dsonmaidinh/Differential-Wheel-Mobile-Robot/firmware/stm/app/app.h

/**
 * @file       app.h
 * @copyright  [Your Copyright]
 * @license    [Your License]
 * @version    1.0.0
 * @date       2026-03-02
 * @author     Dong Son
 *
 * @brief
 */
/* Define to prevent recursive inclusion ------------------------------ */
#ifndef INC_APP_H_
#define INC_APP_H_

/* Includes ----------------------------------------------------------- */
/* Public defines ----------------------------------------------------- */
/* Public enumerate/structure ----------------------------------------- */
/* Public macros ------------------------------------------------------ */
/* Public variables --------------------------------------------------- */
/* Public function prototypes ----------------------------------------- */
uint8_t app_init(void);

uint8_t app_process(void);

#endif /* INC_APP_H_ */

/* End of file -------------------------------------------------------- */
