dsonmaidinh/Differential-Wheel-Mobile-Robot/firmware/stm/sys/sys_task.h

/**
 * @file       sys_task.h
 * @copyright  [Your Copyright]
 * @license    [Your License]
 * @version    0.1.0
 * @date       2026-03-02
 * @author     Dong Son
 *
 * @brief      System Services Task Scheduler using TIM3 interrupt.
 */
/* Define to prevent recursive inclusion ------------------------------ */
#ifndef __SYS_TASK_H
#define __SYS_TASK_H
/* Includes ----------------------------------------------------------- */
#include <stdbool.h>
#include <stdint.h>

/* Public defines ----------------------------------------------------- */
/* Public enumerate/structure ----------------------------------------- */
typedef enum
{
  SRV_TASK_OK = 0,
  SRV_TASK_ERR,
  SRV_TASK_ERR_PARAM
} sys_task_err_t;
typedef void (*sys_task_cb_t)(void *arg);

/* Public macros ------------------------------------------------------ */
/* Public variables --------------------------------------------------- */
/* Public function prototypes ----------------------------------------- */
sys_task_err_t sys_task_init(void);
sys_task_err_t sys_task_process(void);

int            sys_task_add(sys_task_cb_t cb, void *arg, uint32_t period_ms, uint32_t delay_ms);
sys_task_err_t sys_task_del(int id);
sys_task_err_t sys_task_start(int id);
sys_task_err_t sys_task_stop(int id);
sys_task_err_t sys_task_reset(int id);
sys_task_err_t sys_task_set_period(int id, uint32_t period_ms);
sys_task_err_t sys_task_run_now(int id);
bool           sys_task_is_running(int id);
#endif  //__SYS_TASK_H

/* End of file -------------------------------------------------------- */
